stevennguyen/framework/doc/board.png

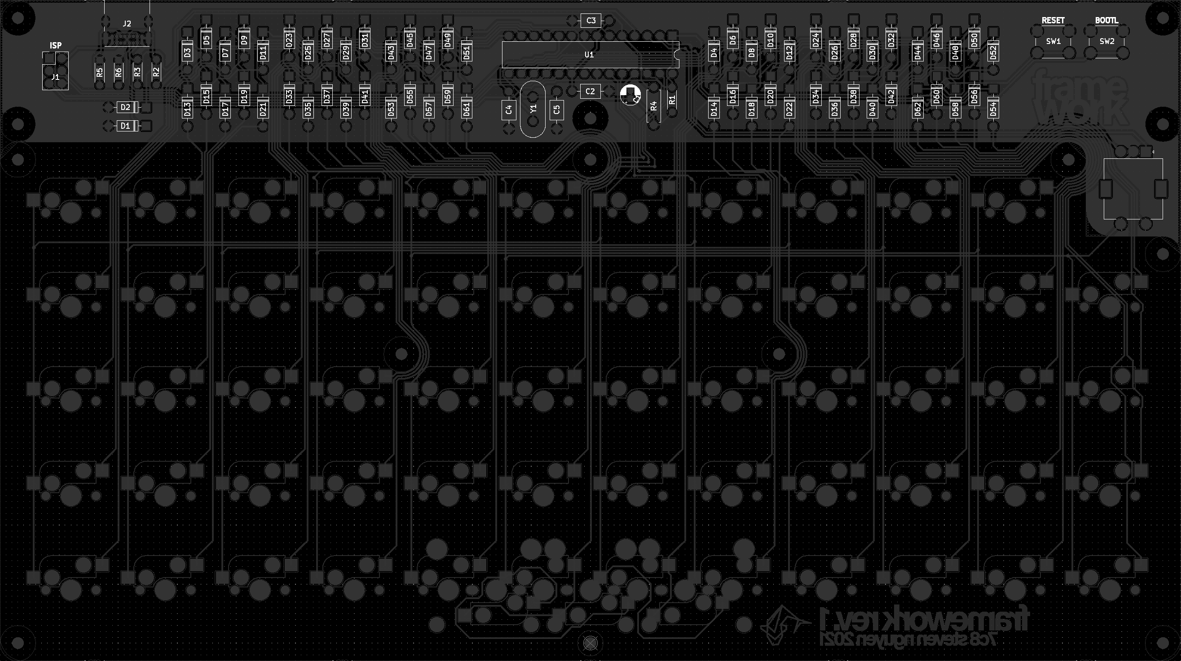
doc/board.png
