stevennguyen/framework/images/oldphotos/1.jpg

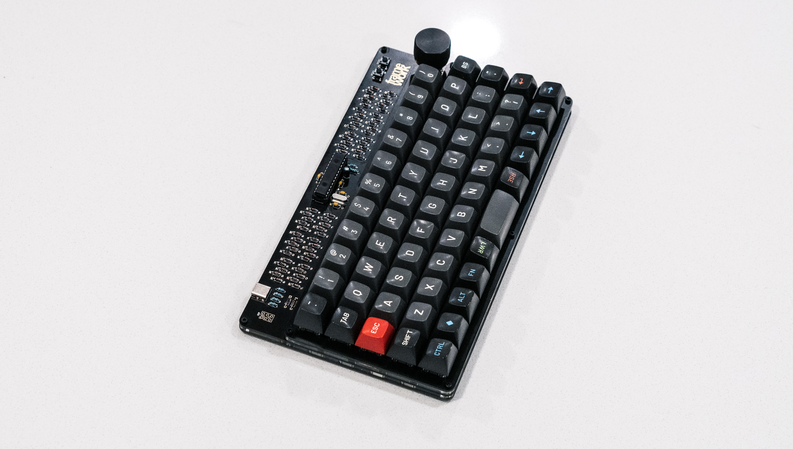
images/oldphotos/1.jpg
