stevennguyen/framework/images/oldphotos/2.jpg

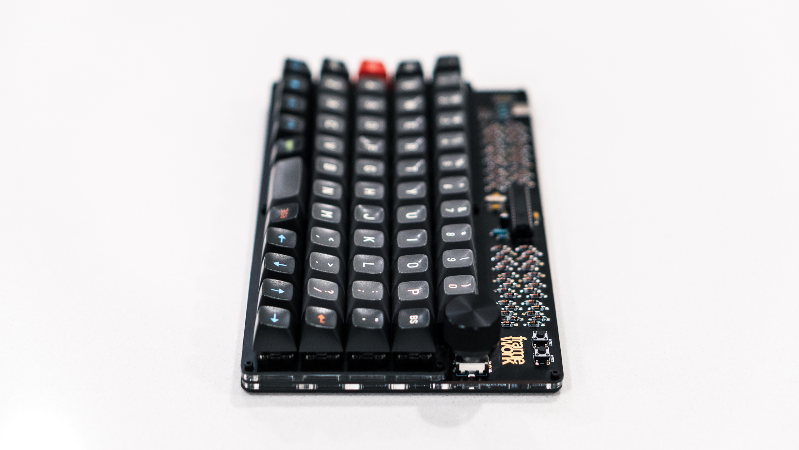
images/oldphotos/2.jpg
