stevennguyen/framework/images/oldphotos/3.jpg

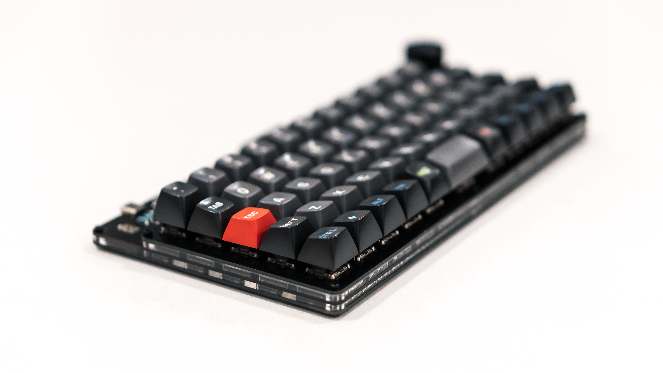
images/oldphotos/3.jpg
