stevennguyen/framework/images/oldphotos/4.jpg

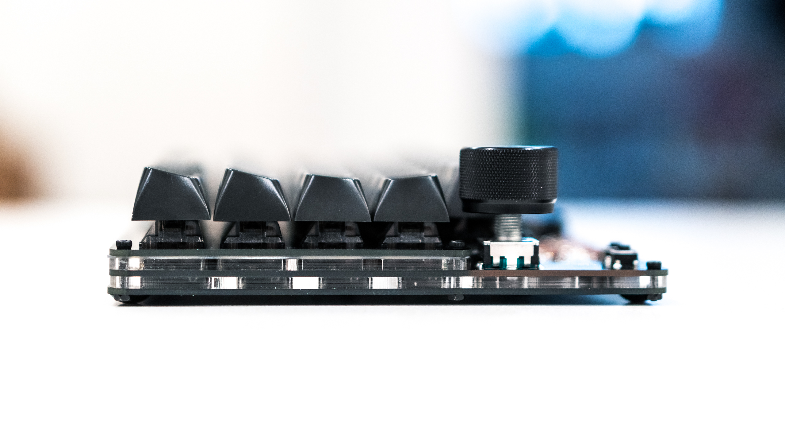
images/oldphotos/4.jpg
