stevennguyen/framework/images/oldphotos/5.jpg

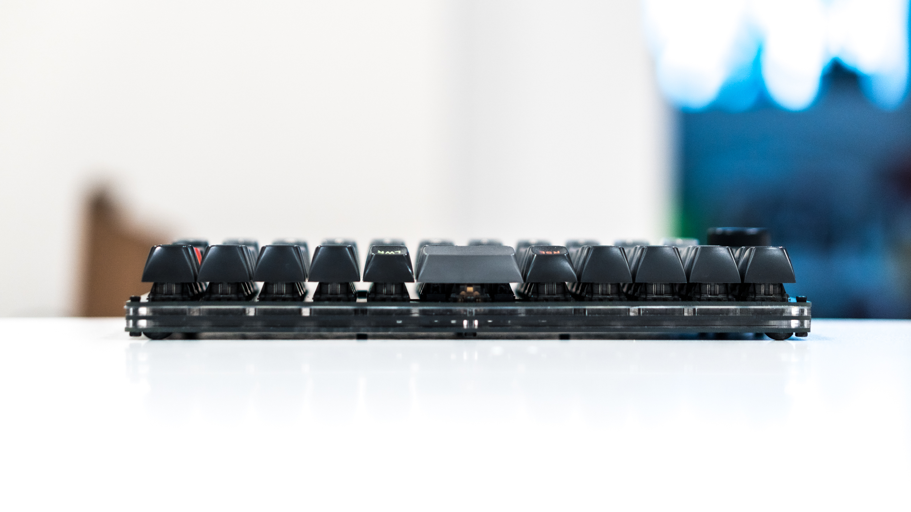
images/oldphotos/5.jpg
